AlvaroRey/P3Steel_V4_20x30/STLs/Eje Z - Soporte EndStop.STEP

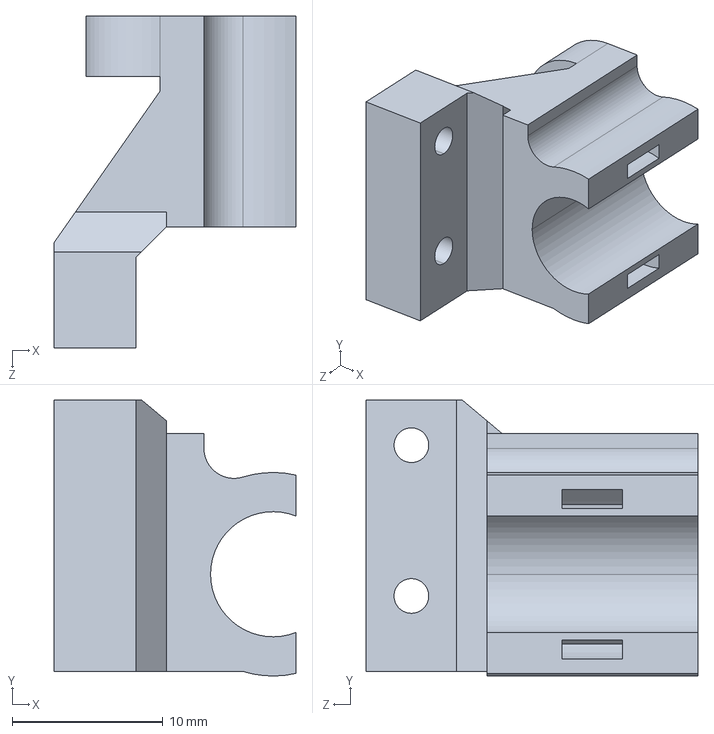
[picture p15: CAD file, 2015-09-07]
STLs/Eje Z - Soporte EndStop.STEP
16.0 x 18.3 x 22.0 mm
