AlvaroRey/P3Steel_V4_20x30/STLs/Eje X - Carro 3 Rodamientos.STL

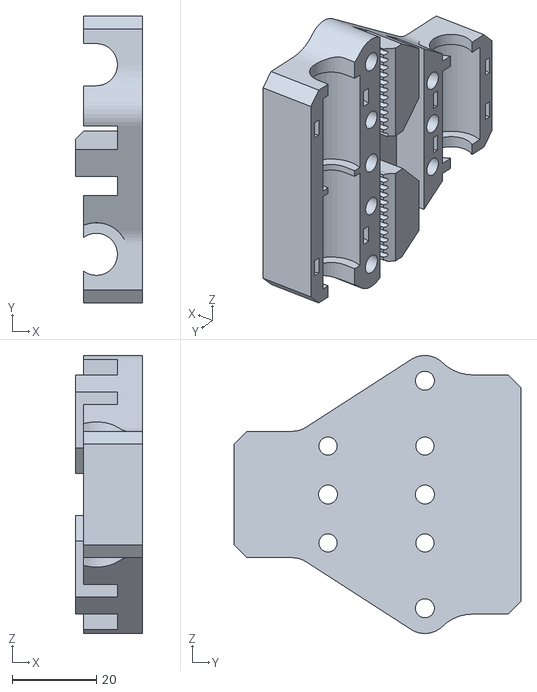
[picture p16: CAD file, 2015-09-07]
STLs/Eje X - Carro 3 Rodamientos.STL
16.0 x 68.0 x 66.0
