AlvaroRey/P3Steel_V4_20x30/STLs/Eje Y - Tensor correa.STEP

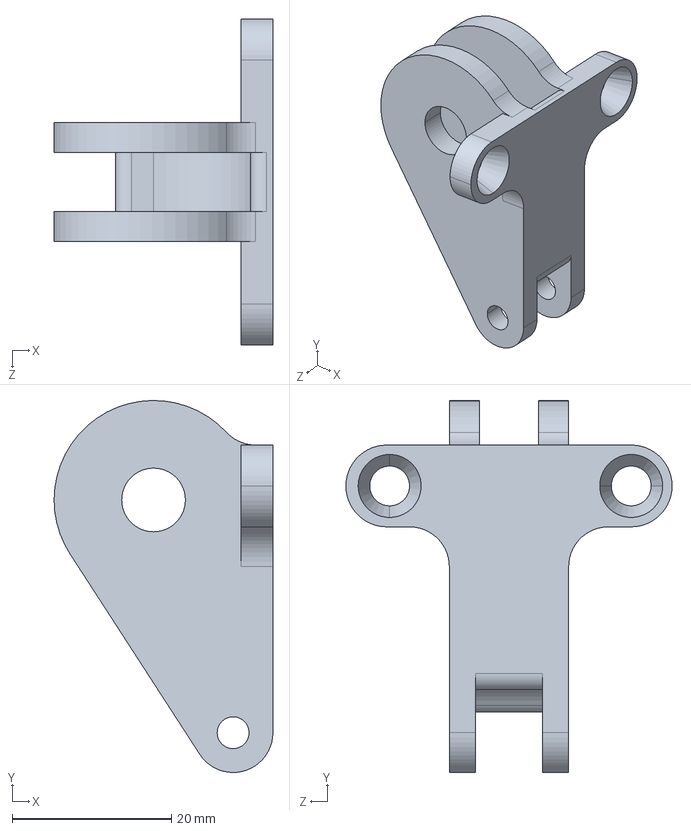
[picture p17: CAD file, 2015-09-07]
STLs/Eje Y - Tensor correa.STEP
27.5 x 46.7 x 41.0 mm
