AlvaroRey/P3Steel_V4_20x30/STLs/Eje X - Tensor Correa.STEP

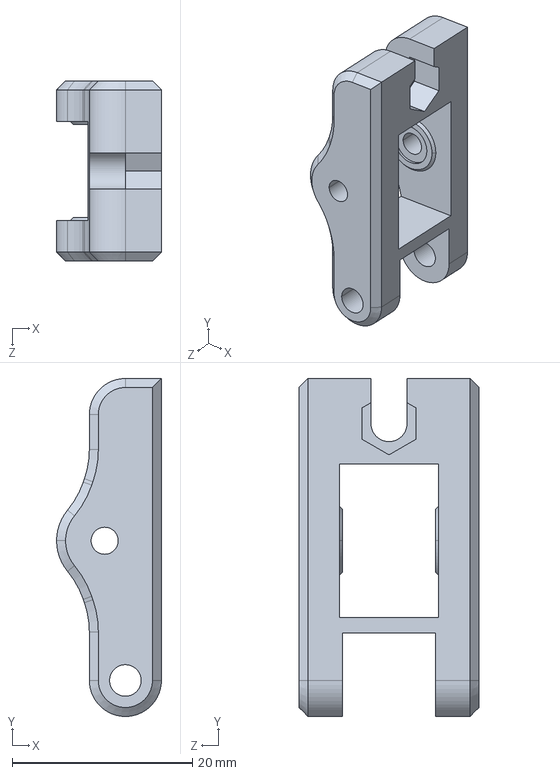
[picture p18: CAD file, 2015-09-07]
STLs/Eje X - Tensor Correa.STEP
11.6 x 37.5 x 20.0 mm
