AlvaroRey/P3Steel_V4_20x30/STLs/Eje X - Soporte Enstop.STEP

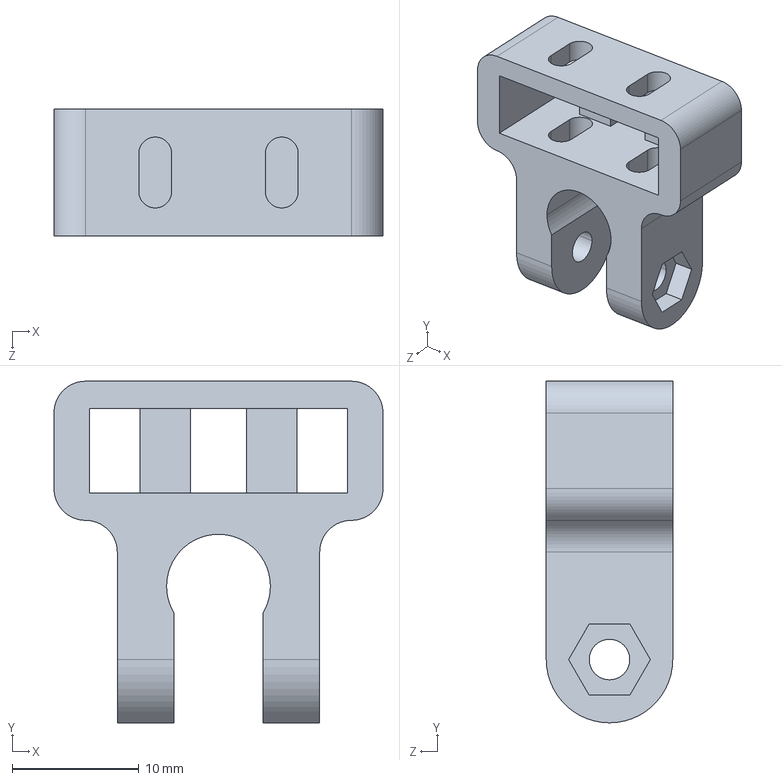
[picture p19: CAD file, 2015-09-07]
STLs/Eje X - Soporte Enstop.STEP
26.0 x 27.0 x 10.0 mm
