AlvaroRey/P3Steel_V4_20x30/STLs/Eje Y - Elevador araña LM10.STEP

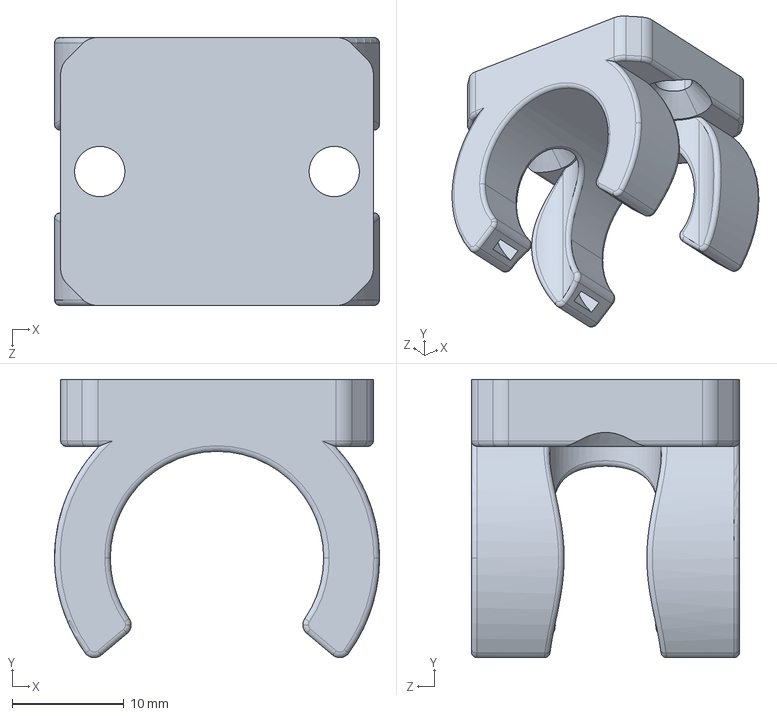
[picture p20: CAD file, 2015-09-07]
STLs/Eje Y - Elevador araña LM10.STEP
29.1 x 24.9 x 24.0 mm
