AlvaroRey/P3Steel_V4_20x30/STLs/Eje Y - Tapas correa.STEP

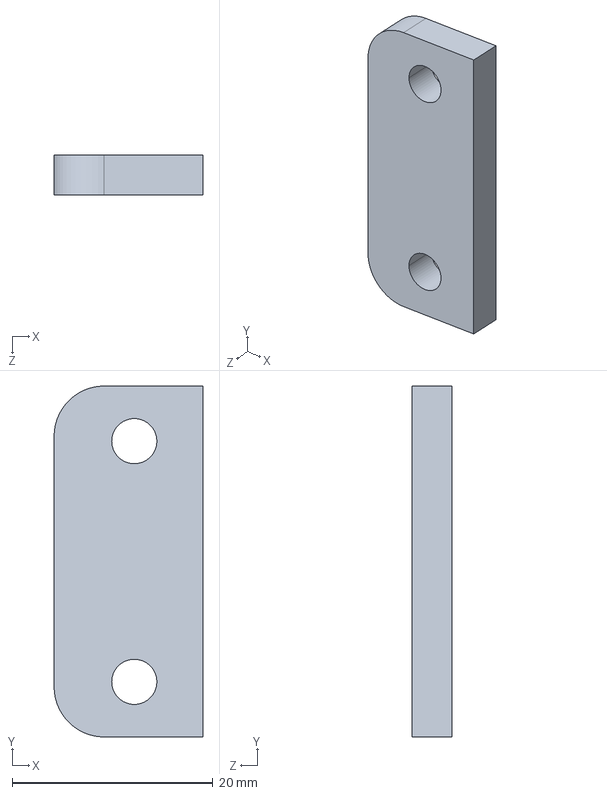
[picture p21: CAD file, 2015-09-07]
STLs/Eje Y - Tapas correa.STEP
14.8 x 35.0 x 4.00 mm
