AlvaroRey/P3Steel_V4_20x30/STLs/Eje Z - Soporte Rodamiento.STEP

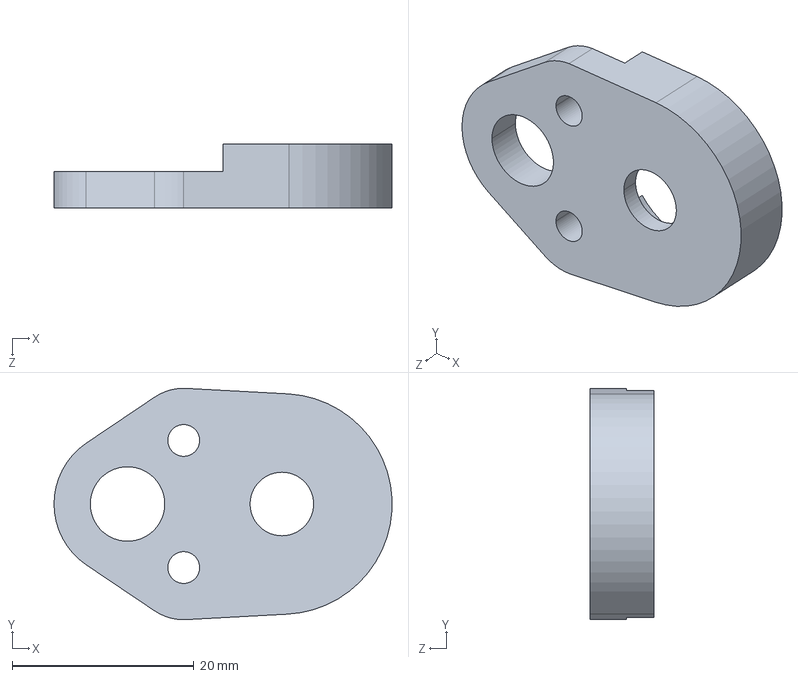
[picture p22: CAD file, 2015-09-07]
STLs/Eje Z - Soporte Rodamiento.STEP
37.2 x 25.5 x 7.00 mm
