AlvaroRey/P3Steel_V4_20x30/STLs/Eje Y - Eje Tensor.STEP

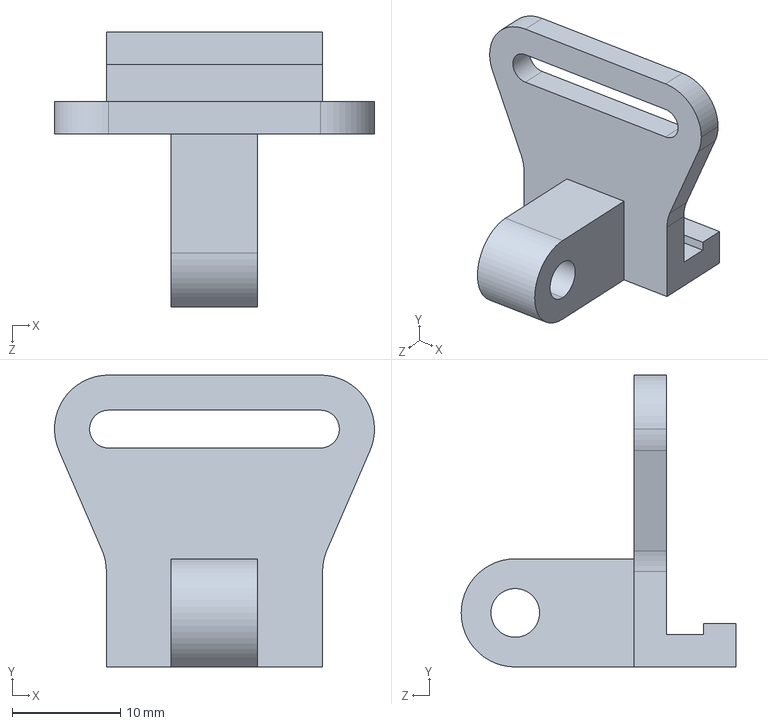
[picture p23: CAD file, 2015-09-07]
STLs/Eje Y - Eje Tensor.STEP
29.6 x 27.0 x 25.4 mm
